mharizanov/new_Funky/examples/LowPowerLab_RF69_lib_test/Struct_send/Struct_send.ino

#include <RFM69.h>
#include <SPI.h>

#define NODEID      99
#define NETWORKID   100
#define GATEWAYID   1
#define FREQUENCY   RF69_868MHZ //Match this with the version of your Moteino! (others: RF69_433MHZ, RF69_868MHZ)
#define KEY         "thisIsEncryptKey" //has to be same 16 characters/bytes on all nodes, not more not less!
#define LED         13
#define SERIAL_BAUD 57600
#define ACK_TIME    50  // # of ms to wait for an ack

int TRANSMITPERIOD = 900; //transmit a packet to gateway so often (in ms)
byte sendSize=0;
boolean requestACK = false;
RFM69 radio;

typedef struct {
  int           nodeId; //store this nodeId
  unsigned long uptime; //uptime in ms
  float         temp;   //temperature maybe?
} Payload;
Payload theData;

void setup() {
  delay(5000);
  Serial.begin(SERIAL_BAUD);
  Serial.println("Starting up");
  pinMode(4,OUTPUT); // Funky v3 RFM12B power control pin
  digitalWrite(4,LOW); //Make sure the RFM12B is on, yes LOW is ON
  delay(100); // Delay (or sleep) to allow the RFM12B to start up
 
  radio.setCS(10);
  radio.initialize(FREQUENCY,NODEID,NETWORKID);
  //radio.setHighPower(); //uncomment only for RFM69HW!
  radio.encrypt(KEY);
  char buff[50];
  sprintf(buff, "\nTransmitting at %d Mhz...", FREQUENCY==RF69_433MHZ ? 433 : FREQUENCY==RF69_868MHZ ? 868 : 915);
  Serial.println(buff);
}

long lastPeriod = -1;
void loop() {
  //process any serial input
  if (Serial.available() > 0)
  {
    char input = Serial.read();
    if (input >= 48 && input <= 57) //[0,9]
    {
      TRANSMITPERIOD = 100 * (input-48);
      if (TRANSMITPERIOD == 0) TRANSMITPERIOD = 1000;
      Serial.print("\nChanging delay to ");
      Serial.print(TRANSMITPERIOD);
      Serial.println("ms\n");
    }
    
    if (input == 'r') //d=dump register values
      radio.readAllRegs();
    //if (input == 'E') //E=enable encryption
    //  radio.encrypt(KEY);
    //if (input == 'e') //e=disable encryption
    //  radio.encrypt(null);
    
  }

  //check for any received packets
  if (radio.receiveDone())
  {
    Serial.print('[');Serial.print(radio.SENDERID, DEC);Serial.print("] ");
    for (byte i = 0; i < radio.DATALEN; i++)
      Serial.print((char)radio.DATA[i]);
    Serial.print("   [RX_RSSI:");Serial.print(radio.readRSSI());Serial.print("]");

    if (radio.ACKRequested())
    {
      radio.sendACK();
      Serial.print(" - ACK sent");
      delay(10);
    }
    Blink(LED,5);
    Serial.println();
  }
  
  int currPeriod = millis()/TRANSMITPERIOD;
  if (currPeriod != lastPeriod)
  {
    //fill in the struct with new values
    theData.nodeId = NODEID;
    theData.uptime = millis();
    theData.temp = 91.23; //it's hot!
    
    Serial.print("Sending struct (");
    Serial.print(sizeof(theData));
    Serial.print(" bytes) ... ");
    if (radio.sendWithRetry(GATEWAYID, (const void*)(&theData), sizeof(theData)))
      Serial.print(" ok!");
    else Serial.print(" nothing...");
    Serial.println();
    Blink(LED,3);
    lastPeriod=currPeriod;
  }
}

void Blink(byte PIN, int DELAY_MS)
{
  pinMode(PIN, OUTPUT);
  digitalWrite(PIN,HIGH);
  delay(DELAY_MS);
  digitalWrite(PIN,LOW);
}
