mharizanov/new_Funky/examples/read_supply_V/read_supply_V.ino

//--------------------------------------------------------------------------------------------------
// Read current supply voltage
//--------------------------------------------------------------------------------------------------
 long readVcc() {
   long result;
   // Read 1.1V reference against Vcc
    ADMUX = _BV(REFS0) | _BV(MUX4) | _BV(MUX3) | _BV(MUX2) | _BV(MUX1);  // For ATmega32u4
   delay(2); // Wait for Vref to settle
   ADCSRA |= _BV(ADSC); // Convert
   while (bit_is_set(ADCSRA,ADSC));
   result = ADCL;
   result |= ADCH<<8;
   result = 1126400L / result; // Back-calculate Vcc in mV
   ADCSRA &= ~ bit(ADEN); 
   return result;
} 
//########################################################################################################################


void setup(){
Serial.begin(9600);
Serial.println("[Atmeg32u4 Read supply voltage]");
}

void loop(){
Serial.println(readVcc());
delay(1000);
}
