mharizanov/new_Funky/examples/Menu_Select/Menu_Select.ino

// SerialConfigMenu.ino - Demo application to show a configuration menu: selection example
// Copyright 2012 Jeroen Doggen (jeroendoggen@gmail.com)
//
// Info:
//      - All strings are stored in program memory to save RAM
//
// Program flow:
//      - Default menu is shown over the serial port
//      - The user types a character to select an option (0, 1 or 2)
//      - A text in printed in the menu (showing the selection)

#include <SerialConfigMenu.h>
SerialConfigMenu Menu;

void setup()
{
  delay(10000);
  Menu.begin(9600);
}

void loop()
{
  Menu.show('d');
  delay(10);                                      //wait for the menu to print
  Menu.readCharBlocking();
  Menu.show('s');
  delay(100);
  Menu.readLine();
  Menu.show('l');
  delay(1000);
}
