mharizanov/new_Funky/examples/Timer_4/coin8.h

/* converted from coin8.raw */
const unsigned char coin8[] PROGMEM = { 0xa0, 0xbe, 0xaf, 0xbd, 0x9c, 0x4d, 0x4a, 0x50, 0x46, 0x8b, 0xbb, 0xa9, 0xb7, 0x9e, 0x56, 0x4e, 0x56, 0x4a, 0x85, 0xb5, 0xa6, 0xb0, 0xa0, 0x5e, 0x51, 0x5a, 0x4f, 0x7f, 0xb0, 0xa3, 0xaa, 0xa0, 0x64, 0x55, 0x5f, 0x54, 0x7a, 0xa9, 0xa0, 0xa4, 0x9e, 0x6a, 0x5a, 0x63, 0x59, 0x77, 0xa3, 0x9c, 0x9e, 0x9c, 0x70, 0x5f, 0x67, 0x5f, 0x75, 0x9c, 0x98, 0x9a, 0x9a, 0x75, 0x61, 0x6a, 0x62, 0x73, 0x9a, 0x99, 0x98, 0x9b, 0x79, 0x62, 0x6a, 0x62, 0x70, 0x98, 0x9a, 0x98, 0x9c, 0x7a, 0x61, 0x69, 0x62, 0x6d, 0x96, 0x9b, 0x97, 0x9d, 0x7e, 0x62, 0x68, 0x65, 0x6b, 0x94, 0x9b, 0x97, 0x9d, 0x81, 0x63, 0x68, 0x65, 0x69, 0x92, 0x9c, 0x96, 0x9d, 0x83, 0x63, 0x68, 0x65, 0x68, 0x8f, 0x9d, 0x96, 0x9e, 0x87, 0x64, 0x66, 0x67, 0x66, 0x8d, 0x9d, 0x95, 0x9d, 0x89, 0x66, 0x66, 0x68, 0x65, 0x89, 0x9c, 0x94, 0x9c, 0x8c, 0x68, 0x66, 0x69, 0x64, 0x85, 0x9d, 0x95, 0x9c, 0x8f, 0x68, 0x66, 0x6a, 0x63, 0x82, 0x9d, 0x95, 0x9c, 0x91, 0x6b, 0x65, 0x6a, 0x62, 0x7f, 0x9c, 0x95, 0x9b, 0x93, 0x6e, 0x65, 0x6a, 0x62, 0x7d, 0x9c, 0x95, 0x9a, 0x96, 0x6f, 0x63, 0x6b, 0x63, 0x79, 0x9c, 0x96, 0x98, 0x96, 0x72, 0x63, 0x6a, 0x62, 0x77, 0x9b, 0x96, 0x98, 0x98, 0x74, 0x63, 0x6a, 0x63, 0x74, 0x9a, 0x98, 0x98, 0x99, 0x78, 0x63, 0x6a, 0x63, 0x71, 0x98, 0x99, 0x97, 0x9b, 0x7b, 0x62, 0x69, 0x63, 0x6e, 0x95, 0x9a, 0x96, 0x9c, 0x7d, 0x62, 0x6a, 0x65, 0x6c, 0x93, 0x9a, 0x95, 0x9c, 0x7f, 0x63, 0x6a, 0x65, 0x6a, 0x92, 0x9b, 0x95, 0x9d, 0x83, 0x64, 0x69, 0x66, 0x68, 0x8f, 0x9c, 0x95, 0x9d, 0x86, 0x65, 0x69, 0x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
const unsigned short coin8_len = 4179;
