mharizanov/new_Funky/examples/temperature_to_RGB/rgb.h

#ifndef RGB_H
#define RGB_H

#include <Arduino.h>
#include <math.h>

class RGB {
  public:
    int red;
    int green;
    int blue;
    
    RGB() 
      : red(0), green(0), blue(0) {
    }
    
    explicit RGB(int brightness) 
      : red(brightness), green(brightness), blue(brightness) {
    }
    
    RGB(int r, int g, int b) 
      : red(r), green(g), blue(b) 
    {
    }
    
    RGB operator+(const RGB& other) {
      return RGB(red + other.red, green + other.green, blue + other.blue);
    }
    
    RGB operator/(int scalar) {
      return RGB(red/scalar, green/scalar, blue/scalar);
    }
};

#define NUM_COLORS 6
#define MAX_TEMP 90.0
#define MIN_TEMP 40.0

RGB colors[NUM_COLORS] = {
  RGB(255, 0, 255), // Purple
  RGB(0, 0, 255), // Blue
  RGB(0, 255, 255), // Cyan
  RGB(0, 255, 0), // Green
  RGB(255, 255, 0), // Yellow
  RGB(255, 0, 0), // Red
};

int interpolate(int col1, int col2, double dx) {
  return (int)((1-dx)*col1 + dx*col2); 
};

RGB interpolate(RGB col1, RGB col2, double dx) {
  RGB rgb(
    interpolate(col1.red, col2.red, dx),
    interpolate(col1.green, col2.green, dx),
    interpolate(col1.blue, col2.blue, dx)
  );
  return rgb;
};

RGB pick_color(int index) {
  index = max(0, min(NUM_COLORS-1, index));
  return colors[index];
}

void print_rgb(RGB rgb) {
  Serial.print("{ ");
  Serial.print(rgb.red);
  Serial.print(", ");
  Serial.print(rgb.green);
  Serial.print(", ");
  Serial.print(rgb.blue);
  Serial.println(" }");
}

RGB color_for_temperature(double t) {
  double normalised = (t-MIN_TEMP)/(MAX_TEMP-MIN_TEMP);
  double col = normalised*(NUM_COLORS-1);
  int col_low = (int)floor(col);
  int col_high = (int)ceil(col);

  double dx = col_high - col;
  if ( t < MIN_TEMP || t > MAX_TEMP ) {
    dx = 0; 
  }

  RGB rgb_high = pick_color(col_high),
      rgb_low  = pick_color(col_low);
  RGB rgb = interpolate(rgb_high, rgb_low, dx);
  //print_rgb(rgb);
  return rgb;
};

#endif // RGB_H
