mharizanov/new_Funky/examples/IR_to_Serial/send_raw_ir.py

#!/usr/bin/python
import serial   ##sudo apt-get install python-serial

print "Sending raw IR sequence.."
ser = serial.Serial('/dev/ttyACM0')
ser.write("SEND 38 1 8450 4150 550 1650 450 1650 500 500 600 450 600 450 600 1550 550 450 600 1550 550 1500 550 1600 550 1550 550 450 600 1600 550 450 550 500 600 450 600 20250 600 1500 650 1500 600 450 600 450 600 450 600 1550 550 450 600 1550 550 1500 600 1500 600 1500 600 450 600 1550 550 450 650 450 500 550 500 20200 600 1500 600 1500 600 450 600 450 550 500 550 1600 550 450 550 1650 550 1500 600 1500 600 1500 600 450 550 1600 550 450 550 500 550 500 550.")
ir=ser.readline()
print ir
ir=ser.readline()
print ir
ir=ser.readline()
print ir
